ZouhirYachou/RGsB_Switcher_IBUS_BMW/images/PXL_20260119_225940429.jpg

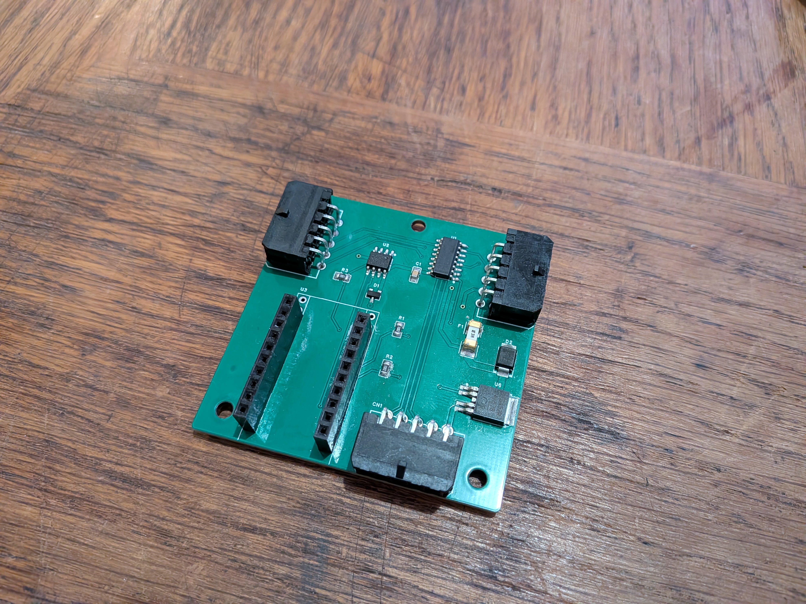
images/PXL_20260119_225940429.jpg
