ZouhirYachou/RGsB_Switcher_IBUS_BMW/images/PXL_20260119_225946828.jpg

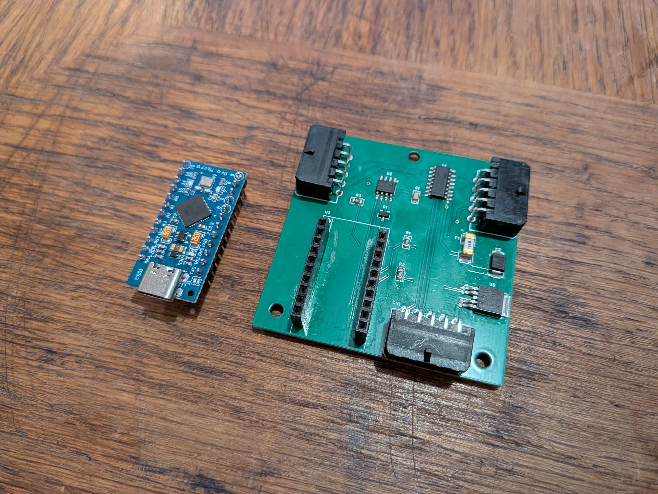
images/PXL_20260119_225946828.jpg
