ZouhirYachou/RGsB_Switcher_IBUS_BMW/images/PXL_20260119_225954938.jpg

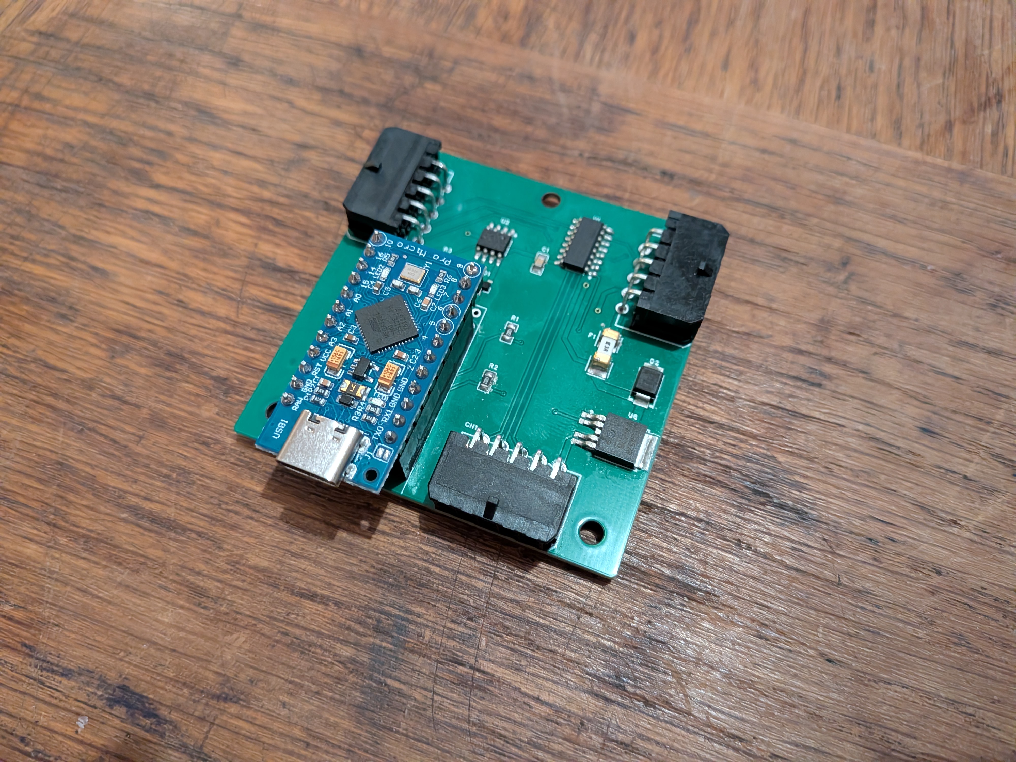
images/PXL_20260119_225954938.jpg
