ZouhirYachou/RGsB_Switcher_IBUS_BMW/images/PXL_20260120_130138552.jpg

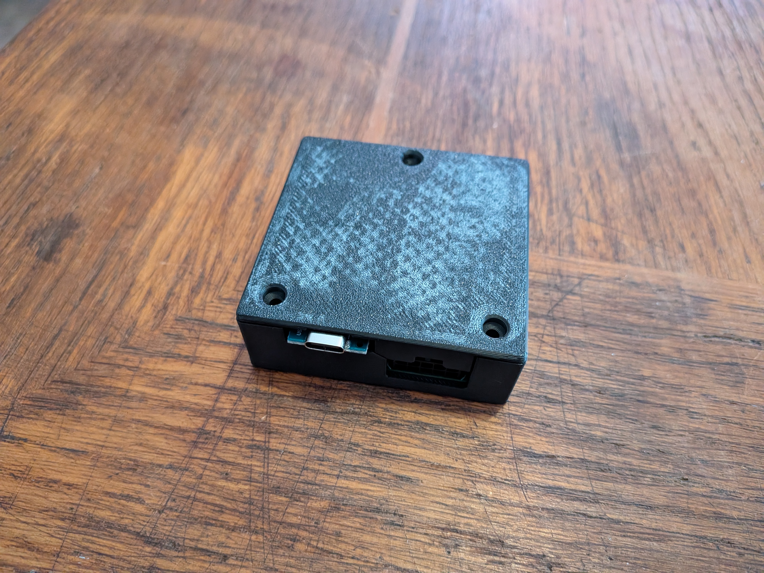
images/PXL_20260120_130138552.jpg
