ZouhirYachou/RGsB_Switcher_IBUS_BMW/images/PXL_20260121_165840646.jpg

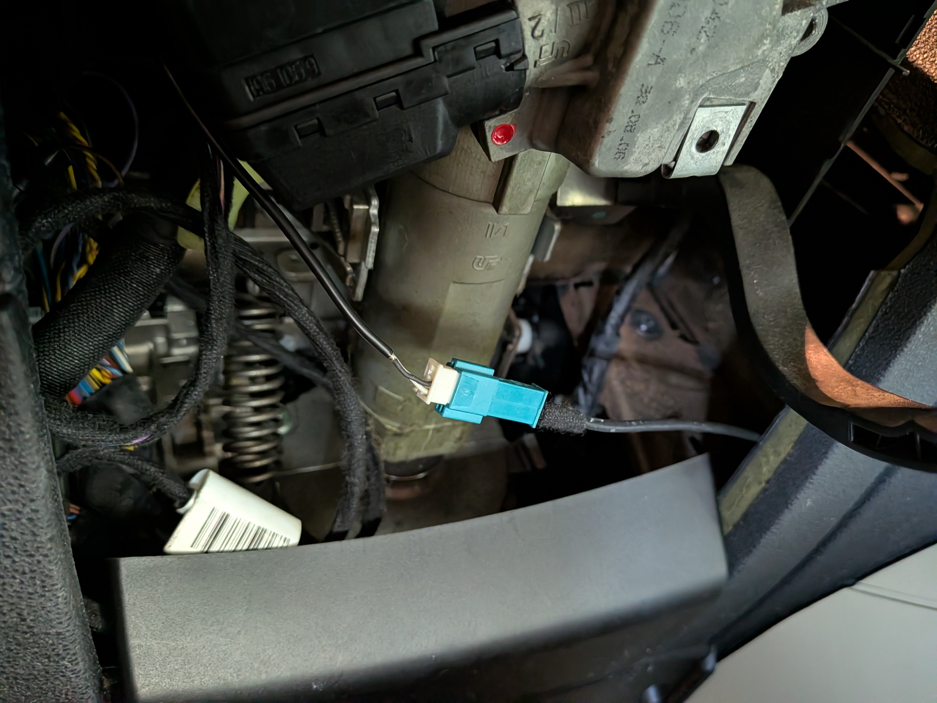
images/PXL_20260121_165840646.jpg
