ZouhirYachou/RGsB_Switcher_IBUS_BMW/images/PXL_20260121_170636377.jpg

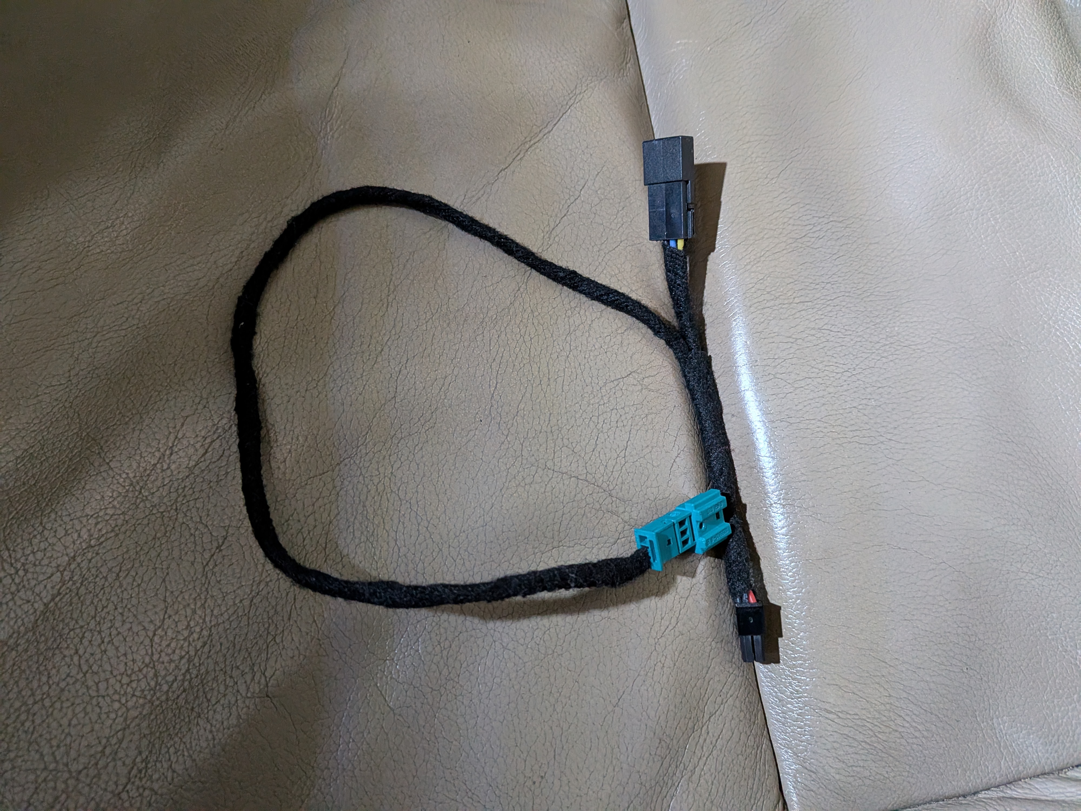
images/PXL_20260121_170636377.jpg
