ZouhirYachou/RGsB_Switcher_IBUS_BMW/images/PXL_20260121_171141101.jpg

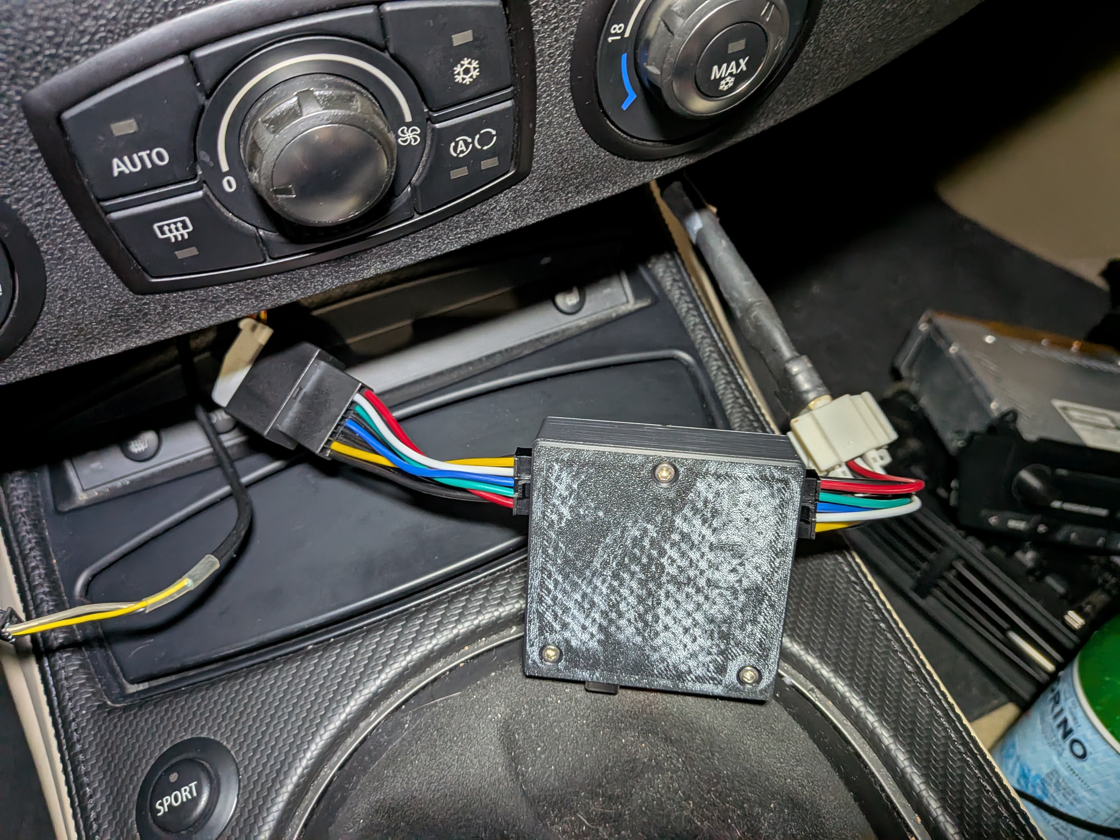
images/PXL_20260121_171141101.jpg
