ZouhirYachou/RGsB_Switcher_IBUS_BMW/images/PXL_20260121_171548791.jpg

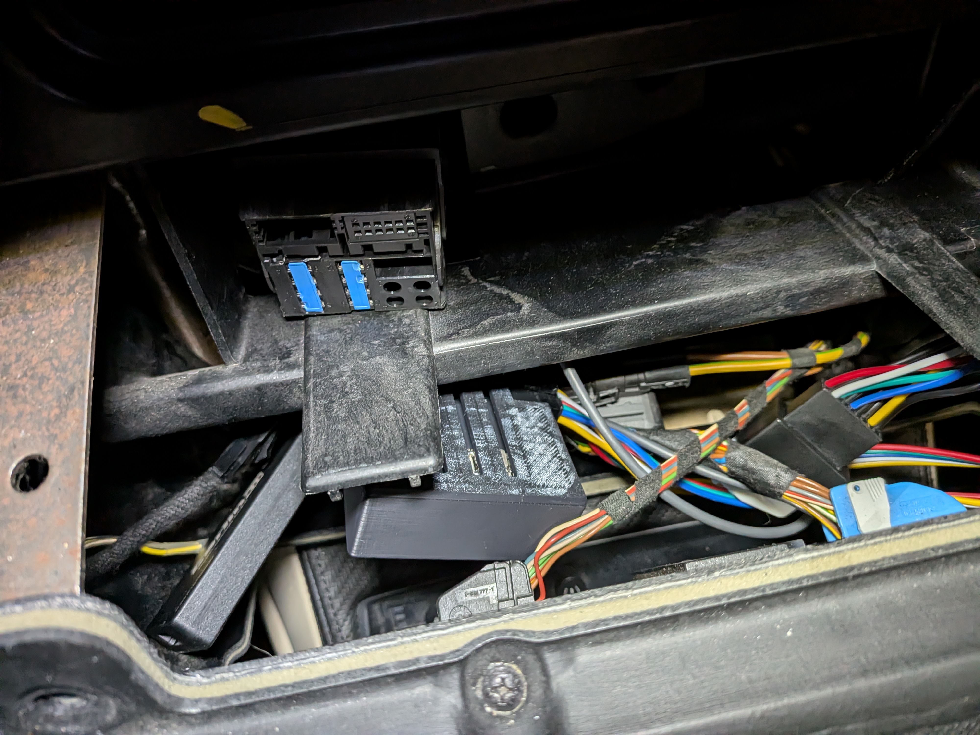
images/PXL_20260121_171548791.jpg
